Quannguyen-0512/Edumaker-STEMkit-/firmware/module-tests/Bluetooth/Bluetooth.ino

#include <SoftwareSerial.h>
SoftwareSerial mySerial(10, 9); 

void setup() {
  Serial.begin(9600);
  Serial.println("Goodnight moon!");

  mySerial.begin(9600);
  mySerial.println("Hello, world?");
}

void loop() { // run over and over
  if (mySerial.available()) {
    Serial.write(mySerial.read());
  }
  if (Serial.available()) {
    mySerial.write(Serial.read());
  }
}
