Quannguyen-0512/Edumaker-STEMkit-/firmware/module-tests/OLED/OLED.ino

#include <Wire.h>
#include <Adafruit_GFX.h>
#include <Adafruit_SSD1306.h>
Adafruit_SSD1306 display(128, 64, &Wire, -1);

void setup() {
  Serial.begin(9600);
  if(!display.begin(SSD1306_SWITCHCAPVCC, 0x3C)) {
    Serial.println(F("SSD1306 allocation failed"));
    for(;;); // Don't proceed, loop forever
  }


}

void loop() {
  display.setTextSize(1);      
  display.setTextColor(SSD1306_WHITE);

  display.clearDisplay();
  display.setCursor(0, 0);  display.print("Hello World"); 
  display.display();
}
