Quannguyen-0512/Edumaker-STEMkit-/firmware/module-tests/Temp_Sensor_mlx9614/Temp_Sensor_mlx9614.ino

#include <Adafruit_MLX90614.h>

Adafruit_MLX90614 mlx = Adafruit_MLX90614();

void setup() {
  Serial.begin(9600);
  while (!Serial);

  Serial.println("Adafruit MLX90614 test");

  if (!mlx.begin()) {
    Serial.println("Error connecting to MLX sensor. Check wiring.");
    while (1);
  };

  Serial.print("Emissivity = "); Serial.println(mlx.readEmissivity());
  Serial.println("================================================");
}

void loop() {
  Serial.print("Ambient = "); Serial.print(mlx.readAmbientTempC());
  Serial.print("*C\tObject = "); Serial.print(mlx.readObjectTempC()); Serial.println("*C");
  Serial.print("Ambient = "); Serial.print(mlx.readAmbientTempF());
  Serial.print("*F\tObject = "); Serial.print(mlx.readObjectTempF()); Serial.println("*F");

  Serial.println();
  delay(500);
}
